magichome/mhip_tracker/doc/images/mhi_tracker_dht.png

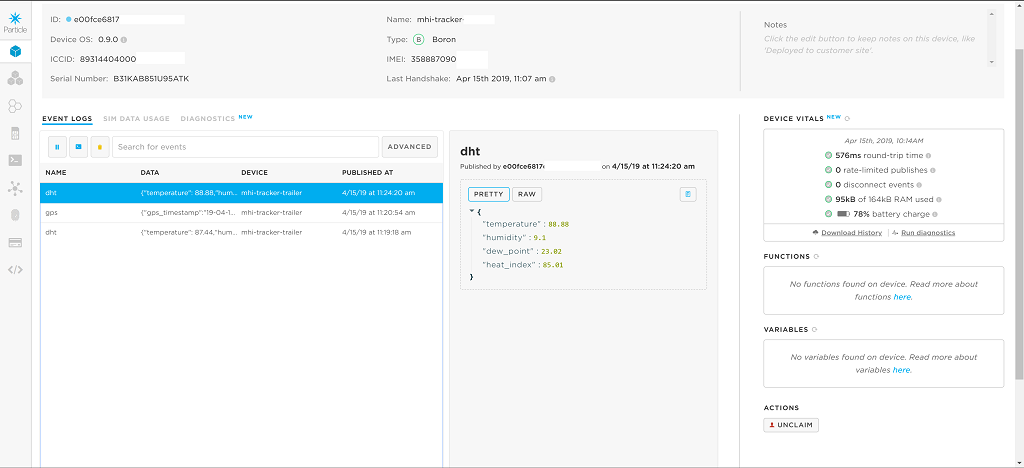
doc/images/mhi_tracker_dht.png
